JeremySCook/JC-Pro-Macro-2/documentation/images/IMAGE 5.png

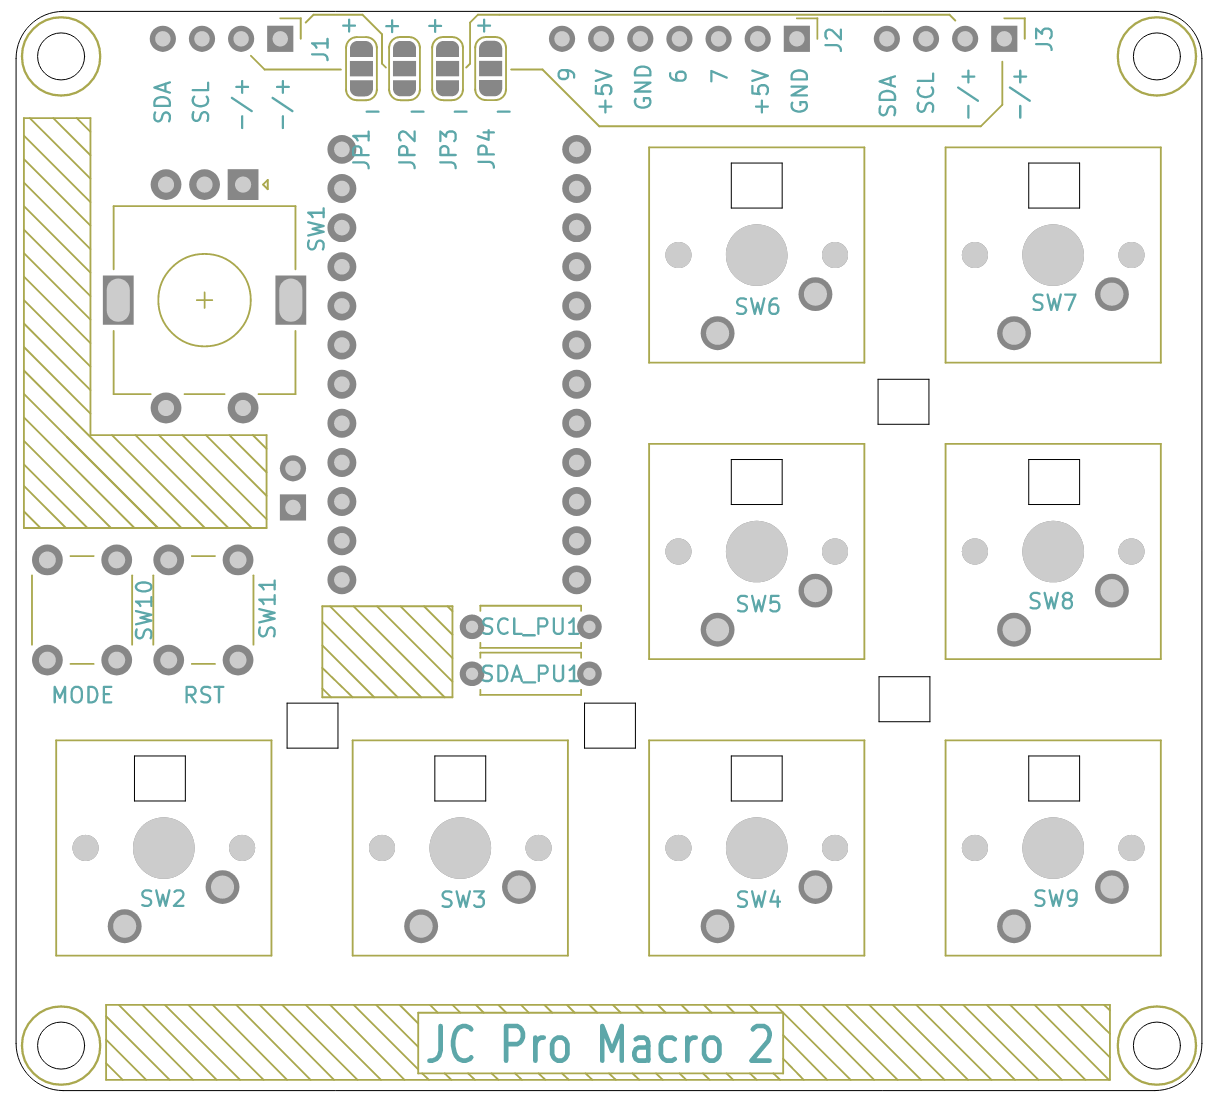
documentation/images/IMAGE 5.png
