JeremySCook/JC-Pro-Macro-2/documentation/images/IMAGE 6.png

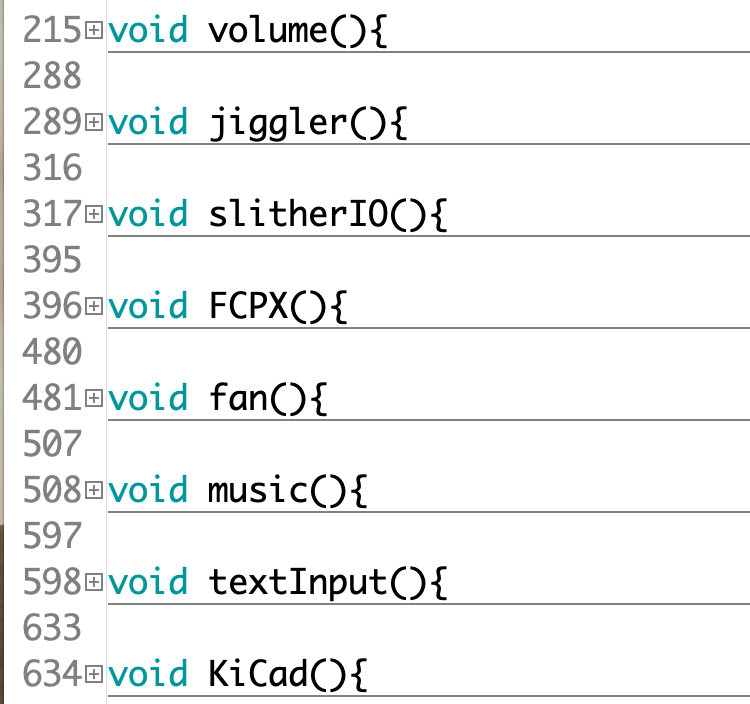
documentation/images/IMAGE 6.png
