JeremySCook/JC-Pro-Macro-2/documentation/images/IMAGE 7.png

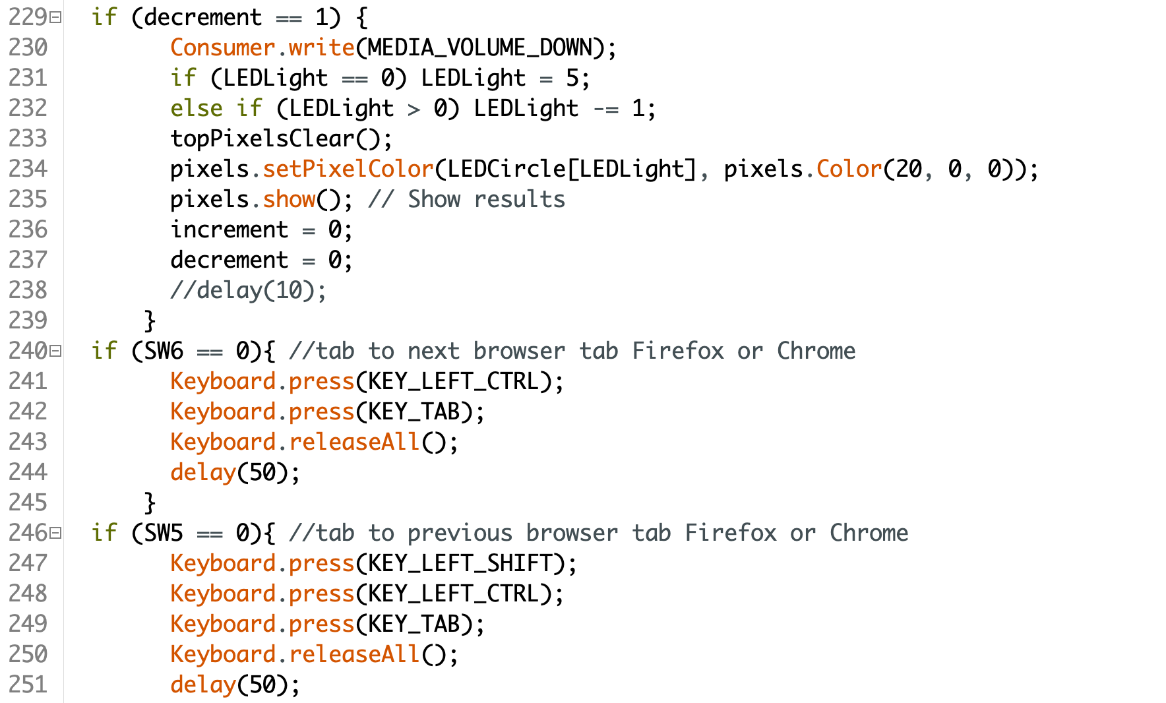
documentation/images/IMAGE 7.png
