JeremySCook/JC-Pro-Macro-2/3DP-accessories/jigs/Jig-ProMicro-Solder.stl

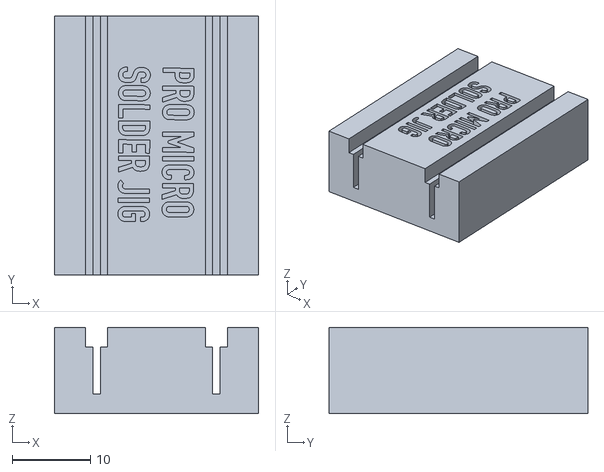
[picture p33: CAD file, 2022-01-27]
3DP-accessories/jigs/Jig-ProMicro-Solder.stl
26.0 x 33.0 x 11.0
