JeremySCook/JC-Pro-Macro-2/3DP-accessories/kureator-case/JCMacro2_Case_V3.step

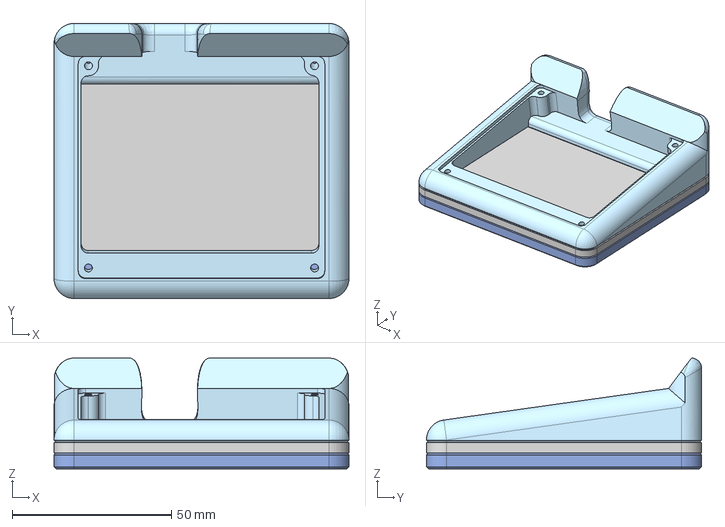
[picture p34: CAD file, 2022-02-26]
3DP-accessories/kureator-case/JCMacro2_Case_V3.step
92.7 x 86.5 x 34.9 mm
